FRC9234/rio2rgb-pcb/macaronsKiCadV2/macaronsV2.kicad_sch

## KiCad design macaronsKiCadV2/macaronsV2.kicad_sch (2024-03-18)

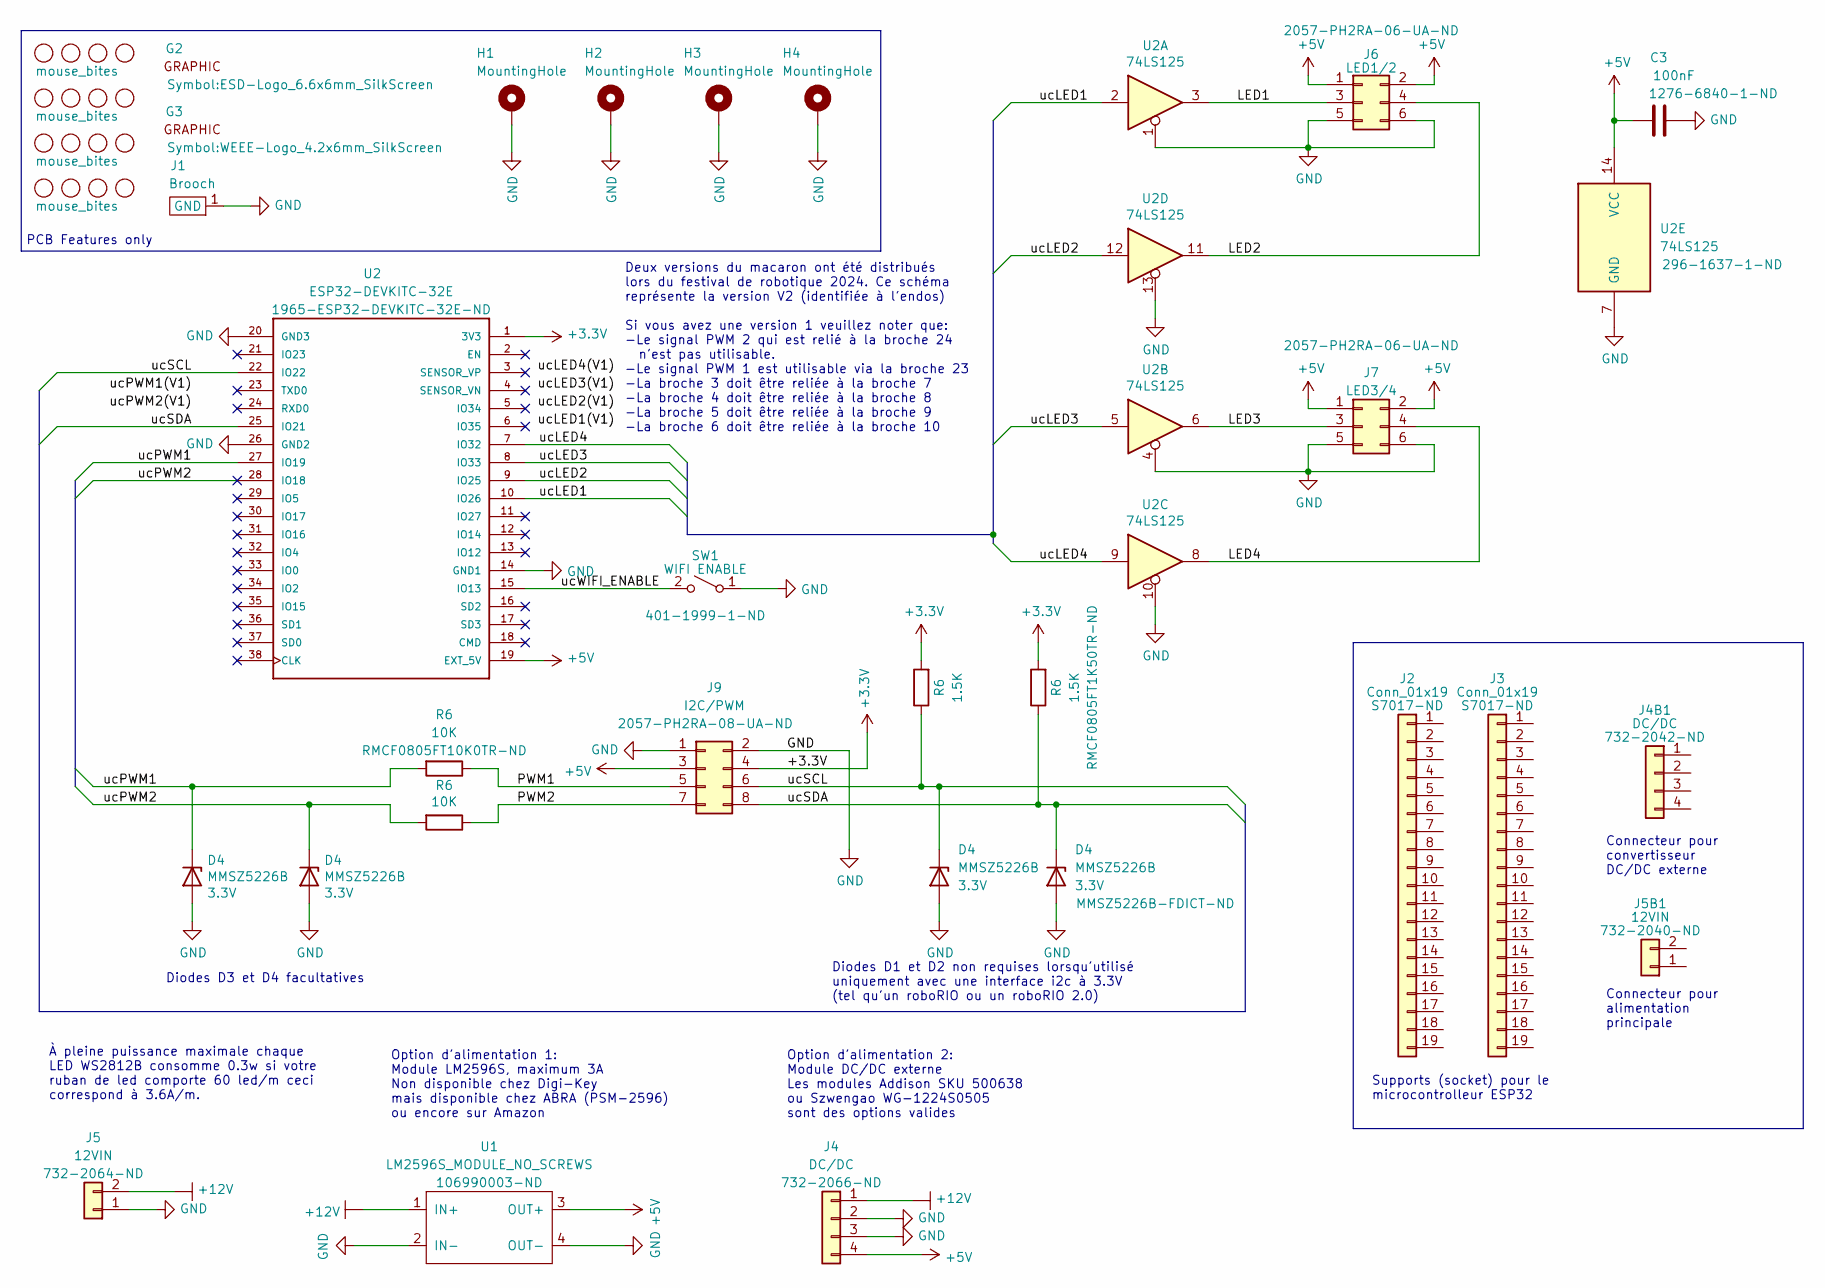
[picture p6: schematic macaronsV2.kicad_sch]

Parts:
C3: 100nF; C_0805_2012Metric_Pad1.18x1.45mm_HandSolder; Digikey PN 1276-6840-1-ND
D4: MMSZ5226B; D_SOD-123; Digikey PN MMSZ5226B-FDICT-ND
G2: ESD-Logo_6.6x6mm_SilkScreen
G3: WEEE-Logo_4.2x6mm_SilkScreen
H1, H2, H3, H4: MountingHole; MountingHole_3.2mm_M3_Pad_Via
J1: Broche_25mm
J2, J3: Conn_01x19; Digikey PN S7017-ND
J4: DC/DC; Würth_691312510004_hangover; Digikey PN 732-2066-ND
J4B1: DC/DC; Digikey PN 732-2042-ND
J5: 12VIN; Würth_691312510002_hangover; Digikey PN 732-2064-ND
J5B1: 12VIN; Digikey PN 732-2040-ND
J6: LED1/2; PinHeader_2x03_P2.54mm_Horizontal; Digikey PN 2057-PH2RA-06-UA-ND
J7: LED3/4; PinHeader_2x03_P2.54mm_Horizontal; Digikey PN 2057-PH2RA-06-UA-ND
J9: I2C/PWM; PinHeader_2x04_P2.54mm_Horizontal; Digikey PN 2057-PH2RA-08-UA-ND
MB1, MB2, MB3, MB4: mouse_bites; mousebite4x
R6: 1.5K; R_0805_2012Metric_Pad1.20x1.40mm_HandSolder; Digikey PN RMCF0805FT1K50TR-ND
SW1: WIFI ENABLE; SW_JS102011SAQN; Digikey PN 401-1999-1-ND
U1: LM2596S_MODULE_NO_SCREWS; LM2596S_MODULE_NO_POST; Digikey PN 106990003-ND
U2: 74LS125; SOIC-14_3.9x8.7mm_P1.27mm; Digikey PN 296-1637-1-ND

Connections:
+3.3V: J9.4, R6.2, U2.1
+5V: C3.2, J4.4, J6.1, J6.2, J7.1, J7.2, J9.3, U1.3 (OUT+), U2.14 (VCC), U2.19 (EXT_5V)
+12V: J4.1, J5.2, U1.1 (IN+)
GND: C3.1, D4.2 (A), H1.1, H2.1, H3.1, H4.1, J1.1, J4.2, J4.3, J5.1, J6.5, J6.6, J7.5, J7.6, J9.1, J9.2, SW1.1 (A), U1.2 (IN-), U1.4 (OUT-), U2.1, U2.4, U2.7 (GND), U2.10, U2.13, U2.14 (VCC), U2.20 (GND3), U2.26 (GND2)
LED1: J6.3, U2.3
LED2: J6.4, U2.11
LED3: J7.3, U2.6
LED4: J7.4, U2.8
PWM1: J9.5, R6.1
PWM2: J9.7, R6.1
ucLED1: U2.2, U2.10
ucLED2: U2.9, U2.12
ucLED3: U2.5, U2.8
ucLED4: U2.7 (GND), U2.9
ucPWM1: D4.1 (K), R6.2, U2.27 (IO19)
ucPWM2: D4.1 (K), R6.2, U2.28 (IO18)
ucSCL: D4.1 (K), J9.6, R6.1, U2.22 (IO22)
ucSDA: D4.1 (K), J9.8, R6.1, U2.25 (IO21)
ucWIFI_ENABLE: SW1.2 (B), U2.15 (IO13)

Notes on the sheet:
Diodes D3 et D4 facultatives
Supports (socket) pour le microcontrolleur ESP32
PCB Features only
Connecteur pour convertisseur DC/DC externe
Deux versions du macaron ont été distribués lors du festival de robotique 2024. Ce schéma représente la version V2 (identifiée à l'endos) Si vous avez une version 1 veuillez noter que: -Le signal PWM 2 qui est relié à la broche 24 n'est pas utilisable. -Le signal PWM 1 est utilisable via la broche 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
Diodes D1 et D2 non requises lorsqu'utilisé uniquement avec une interface i2c à 3.3V (tel qu'un roboRIO ou un roboRIO 2.0)
À pleine puissance maximale chaque LED WS2812B consomme 0.3w si votre ruban de led comporte 60 led/m ceci correspond à 3.6A/m.
Option d'alimentation 1: Module LM2596S, maximum 3A Non disponible chez Digi-Key mais disponible chez ABRA (PSM-2596) ou encore sur Amazon
Option d'alimentation 2: Module DC/DC externe Les modules Addison SKU 500638 ou Szwengao WG-1224S0505 sont des options valides
Connecteur pour alimentation principale
